Squonk42/USBug/CAM/D43324.TXT.pdf

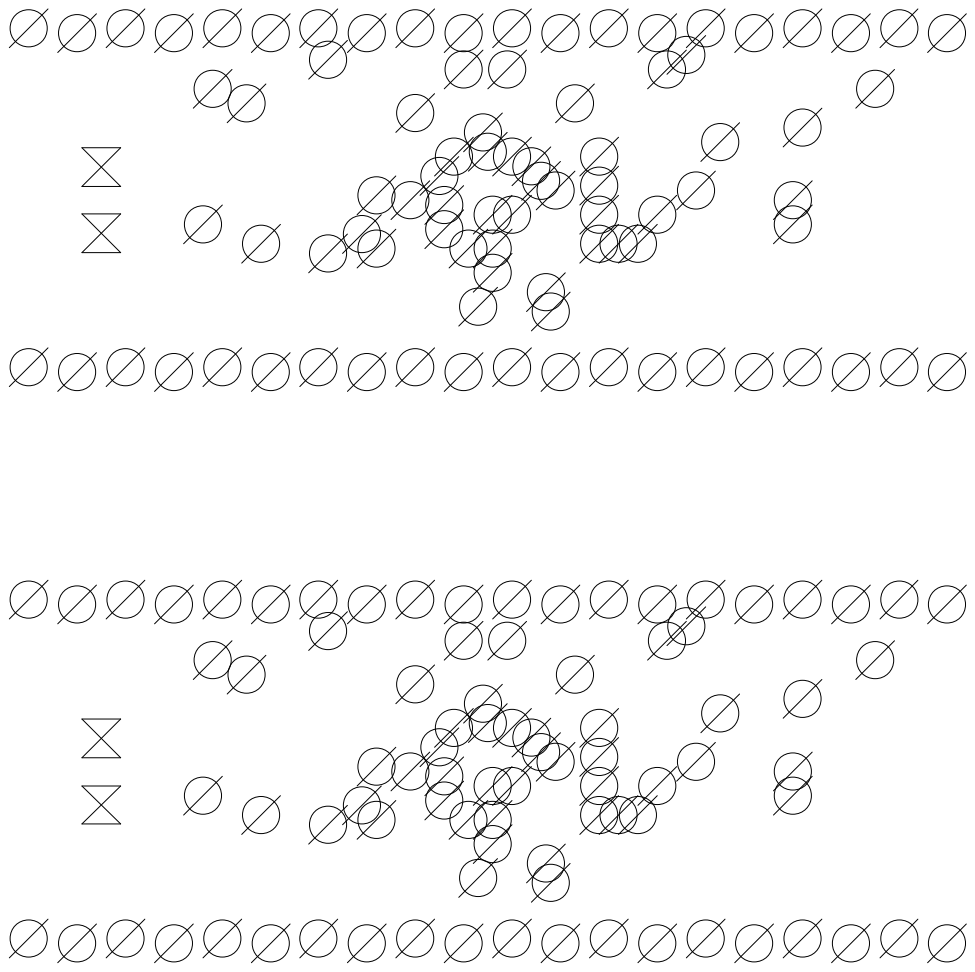
[picture p5: page 1]
