Squonk42/USBug/CAM/D43324.png

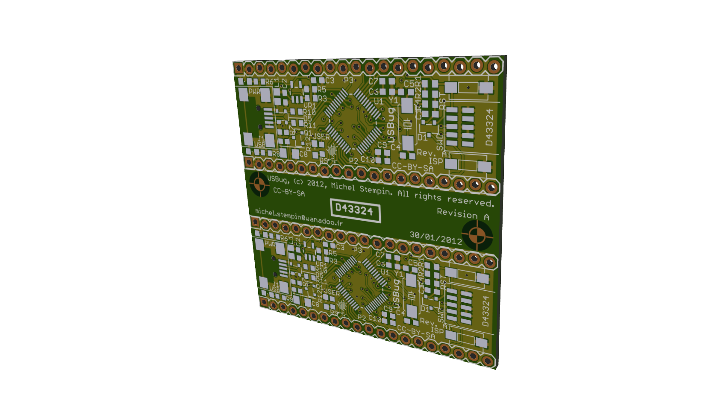
CAM/D43324.png
