Squonk42/USBug/eagleUp/Board-Comparison.jpg

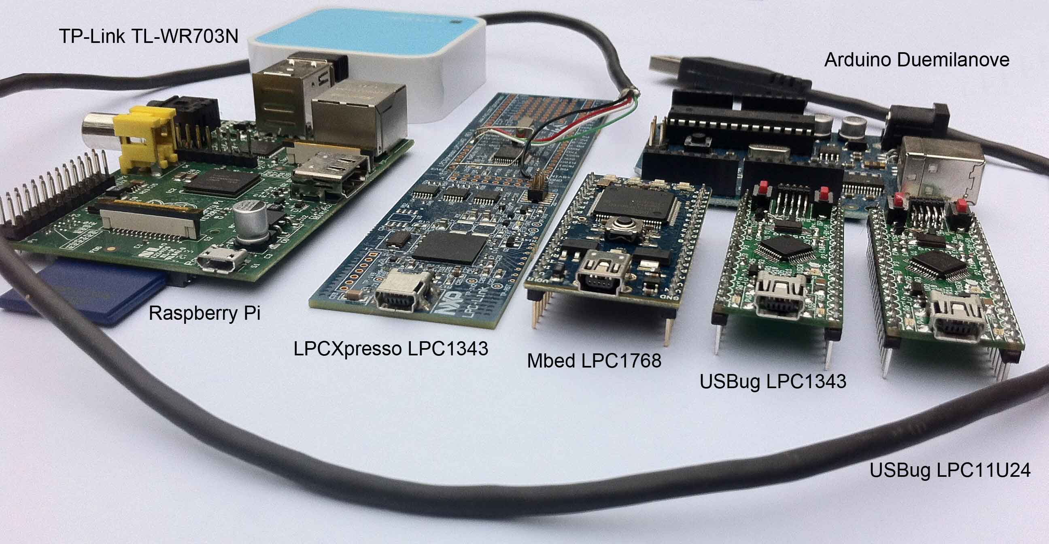
eagleUp/Board-Comparison.jpg
