Squonk42/USBug/eagleUp/eagleUp_USBug_board_bottom.jpg

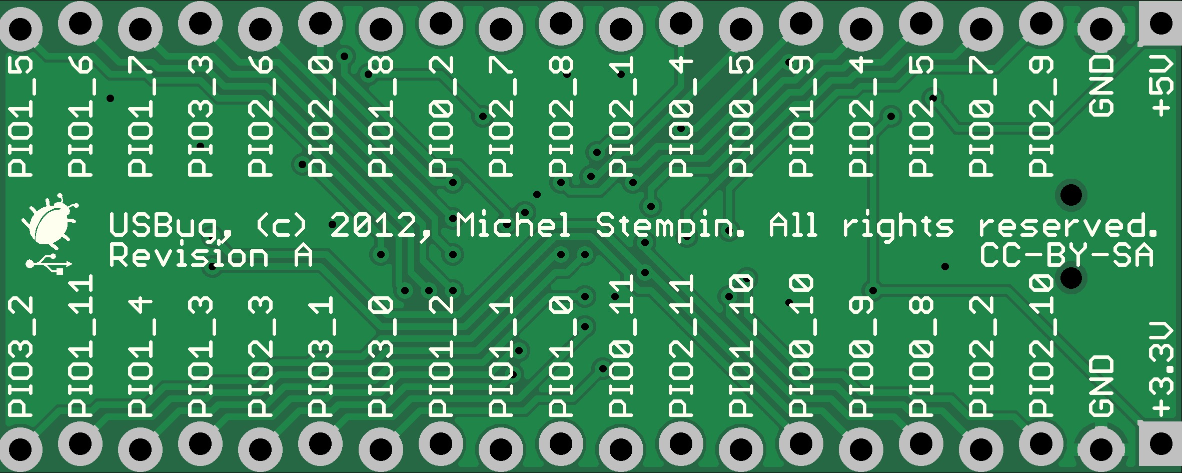
eagleUp/eagleUp_USBug_board_bottom.jpg
