Squonk42/USBug/eagleUp/eagleUp_USBug_board_bottom.png

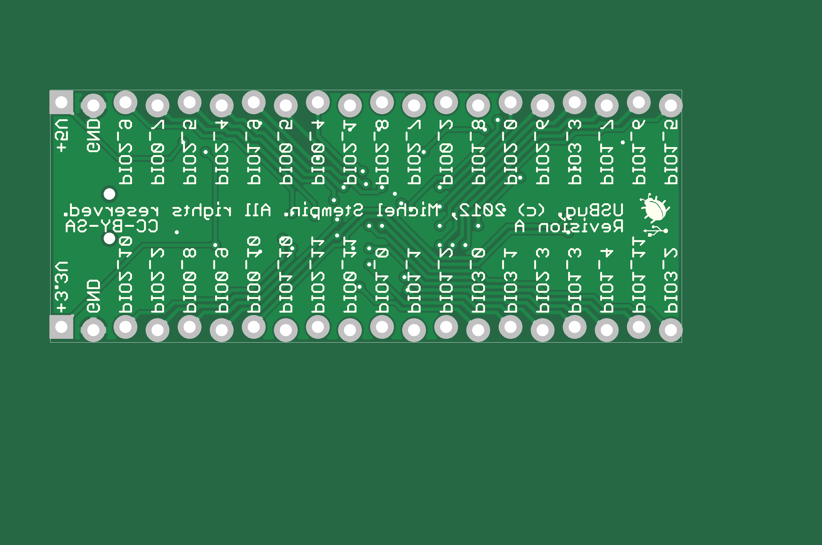
eagleUp/eagleUp_USBug_board_bottom.png
