Squonk42/USBug/eagleUp/eagleUp_USBug_board_top.jpg

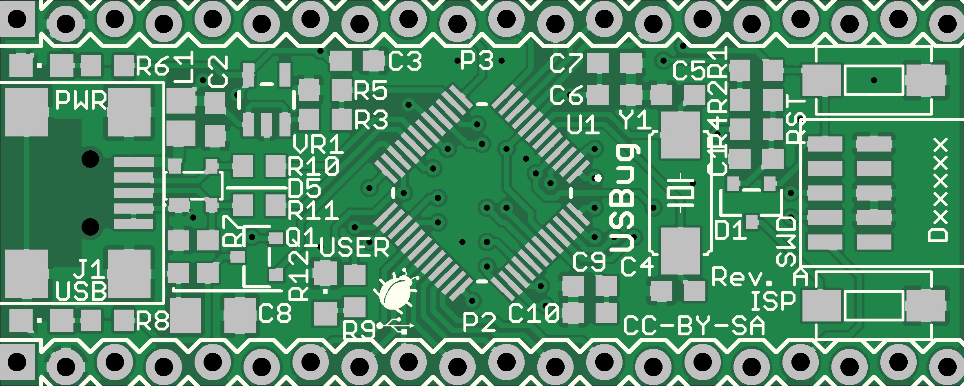
eagleUp/eagleUp_USBug_board_top.jpg
