Squonk42/USBug/eagleUp/eagleUp_USBug_board_top.png

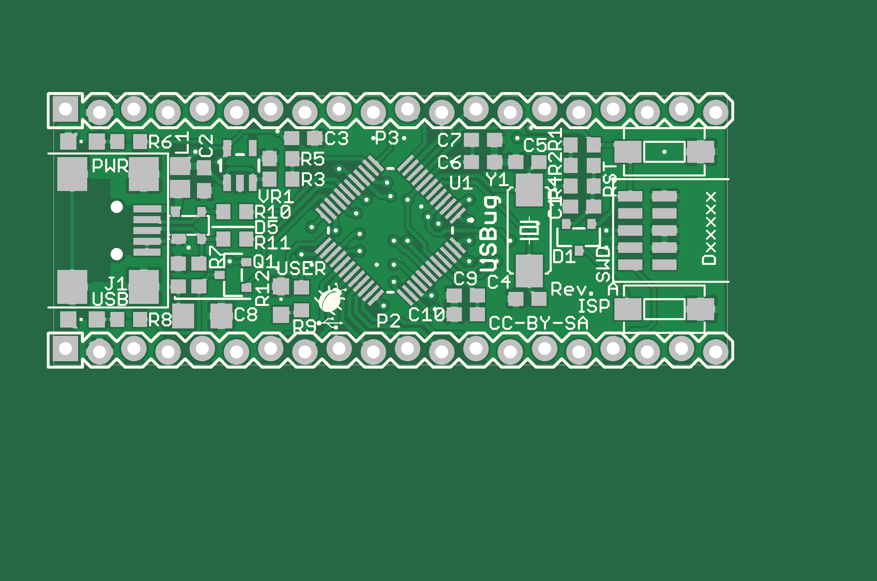
eagleUp/eagleUp_USBug_board_top.png
