Squonk42/USBug/eagleUp/eagleUp_USBug_bottom.png

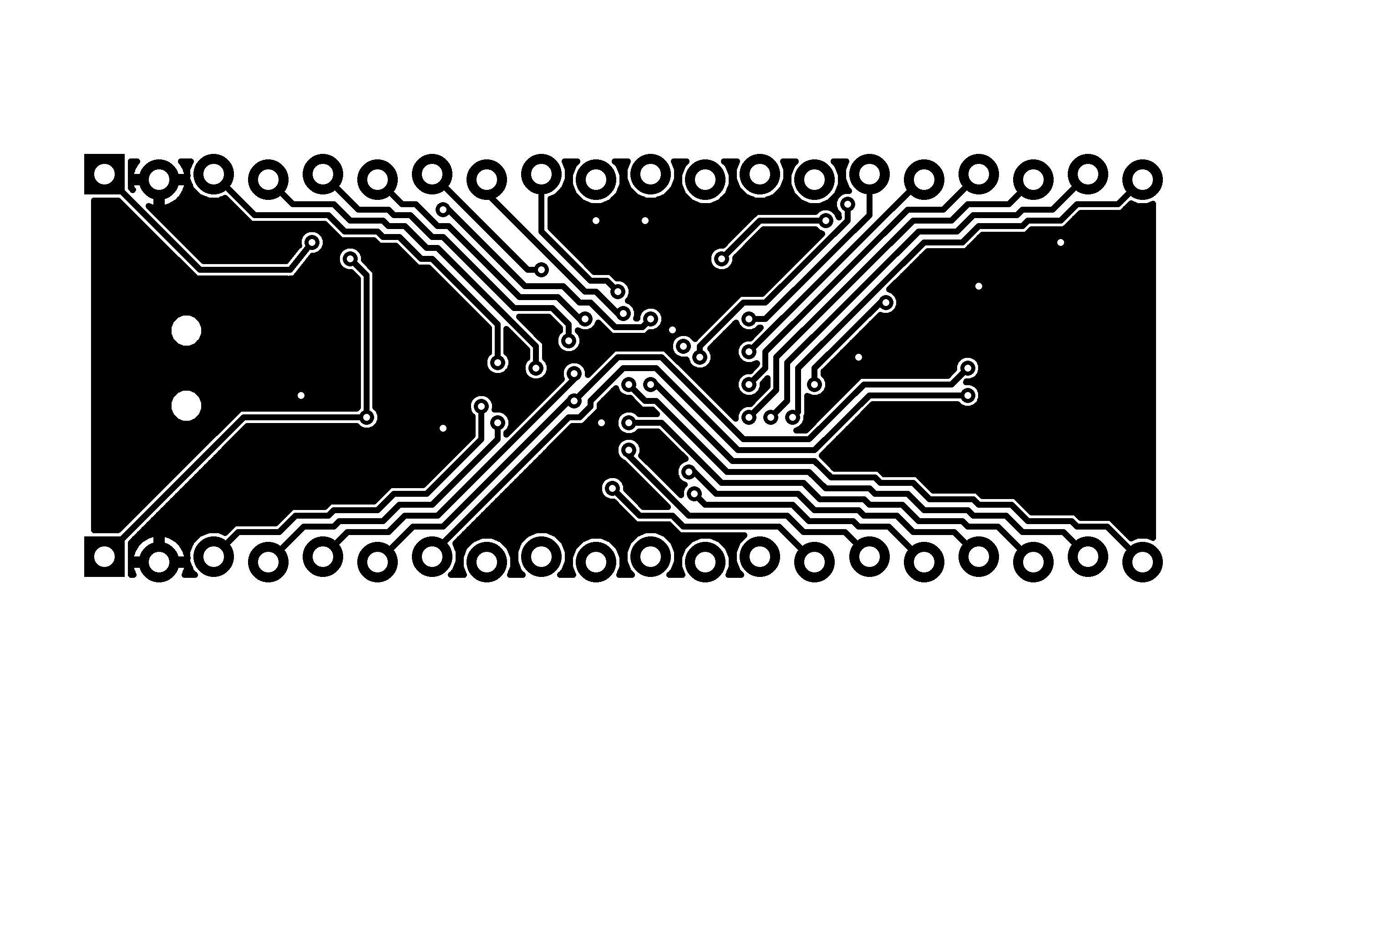
eagleUp/eagleUp_USBug_bottom.png
