Squonk42/USBug/eagleUp/eagleUp_USBug_bottom_mask.png

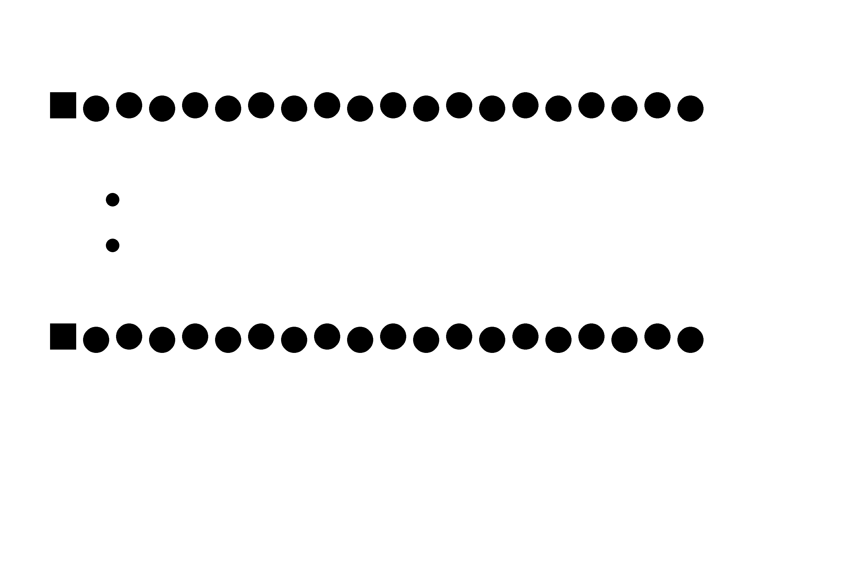
eagleUp/eagleUp_USBug_bottom_mask.png
