Squonk42/USBug/eagleUp/eagleUp_USBug_bottom_silk.png

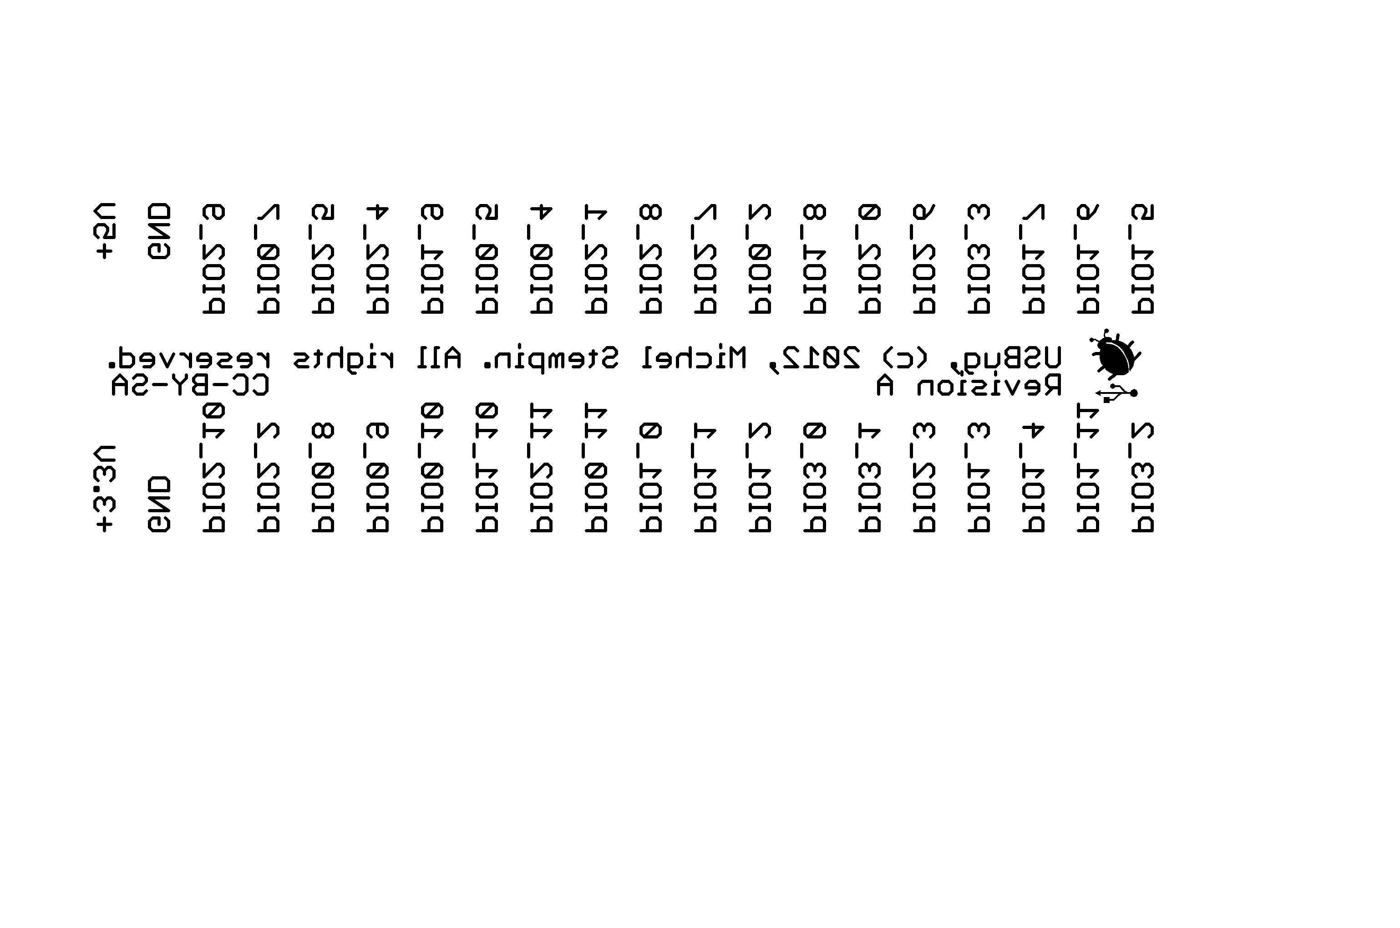
eagleUp/eagleUp_USBug_bottom_silk.png
