Squonk42/USBug/eagleUp/eagleUp_USBug_drill.png

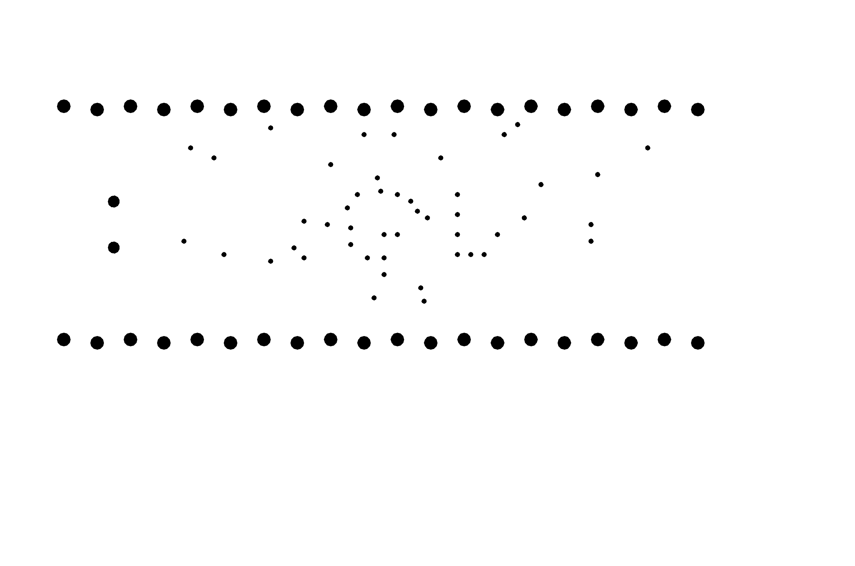
eagleUp/eagleUp_USBug_drill.png
