Squonk42/USBug/eagleUp/eagleUp_USBug_imagesize.png

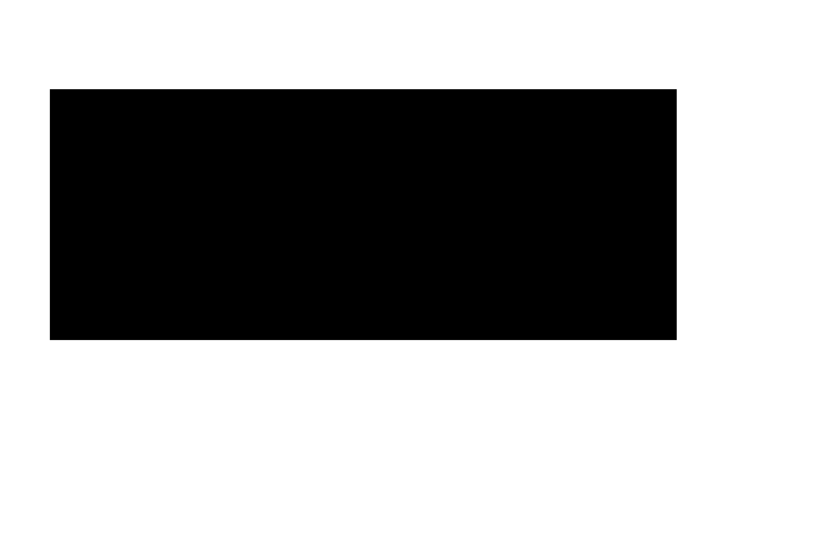
eagleUp/eagleUp_USBug_imagesize.png
