Squonk42/USBug/eagleUp/eagleUp_USBug_outline.png

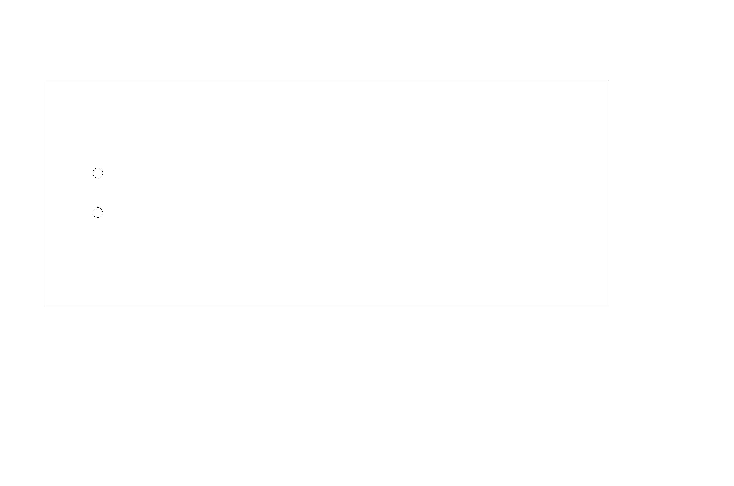
eagleUp/eagleUp_USBug_outline.png
