Squonk42/USBug/eagleUp/eagleUp_USBug_top.png

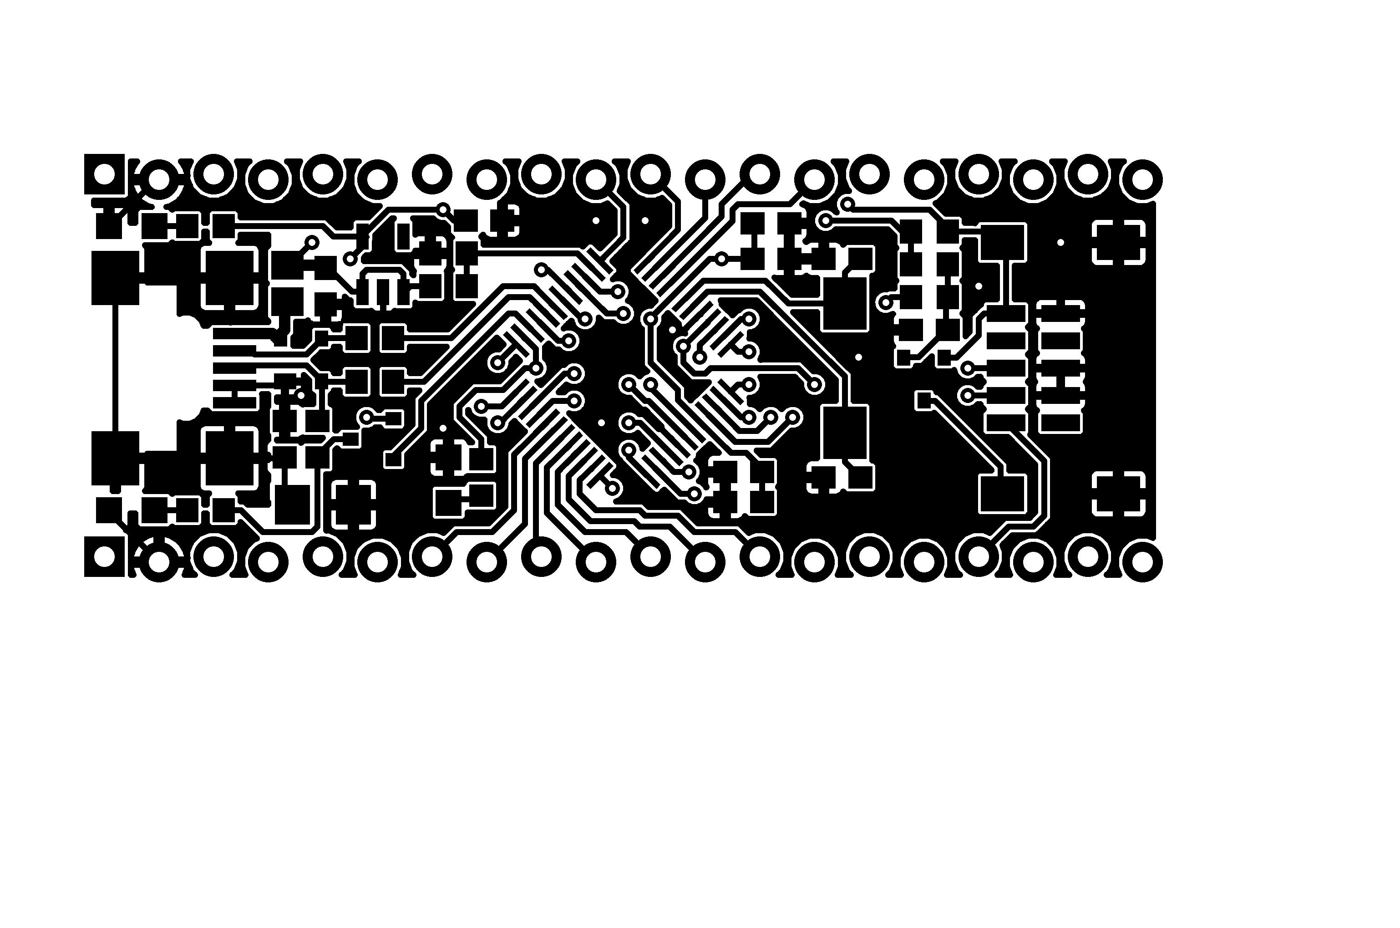
eagleUp/eagleUp_USBug_top.png
