Squonk42/USBug/eagleUp/eagleUp_USBug_top_mask.png

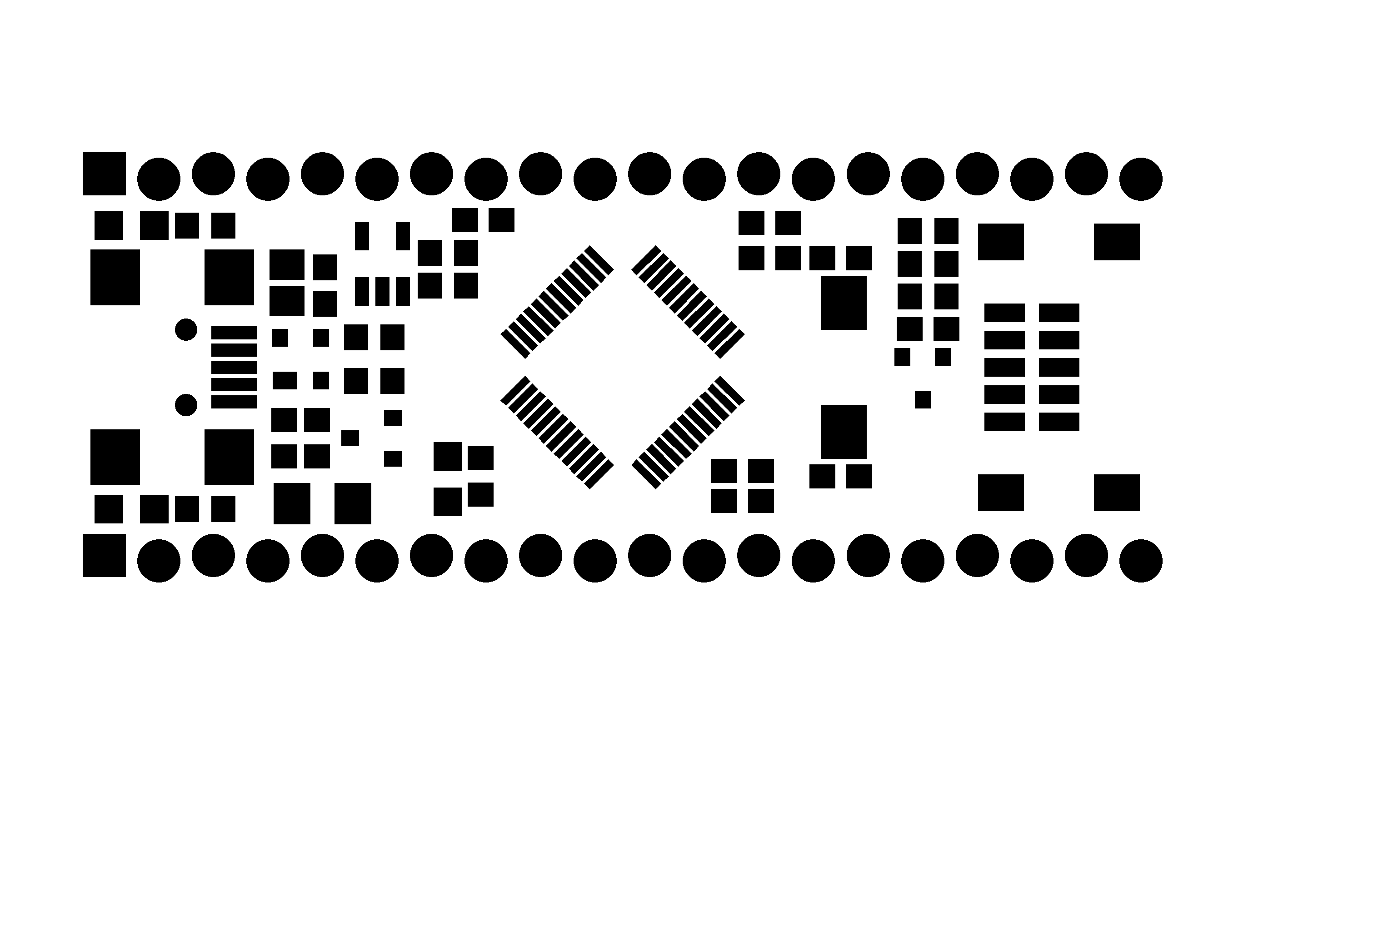
eagleUp/eagleUp_USBug_top_mask.png
