Squonk42/USBug/eagleUp/eagleUp_USBug_top_silk.png

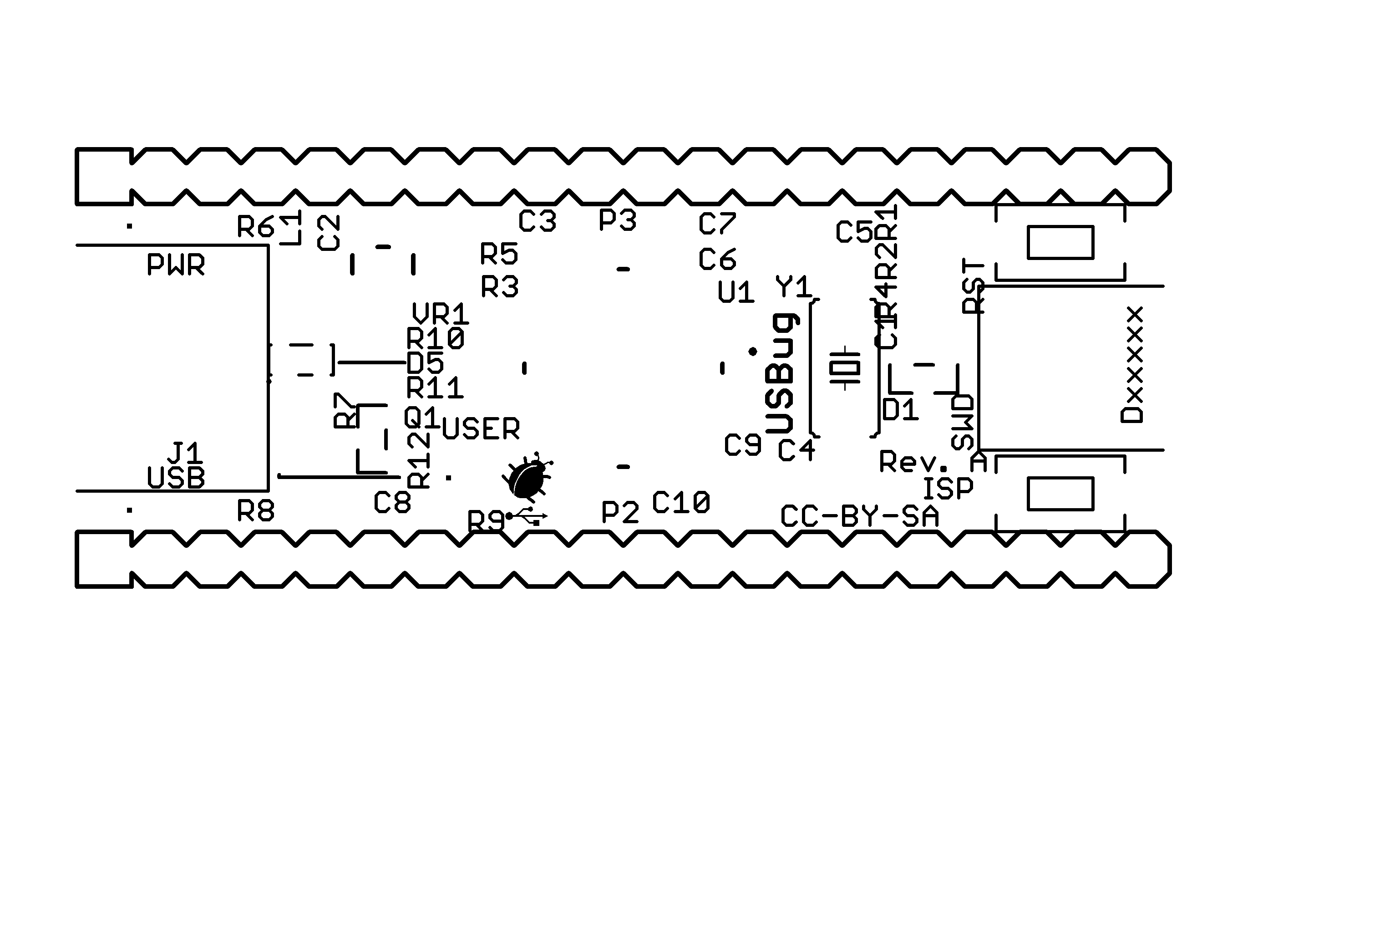
eagleUp/eagleUp_USBug_top_silk.png
