Squonk42/USBug/eagleUp/USBug1.jpg

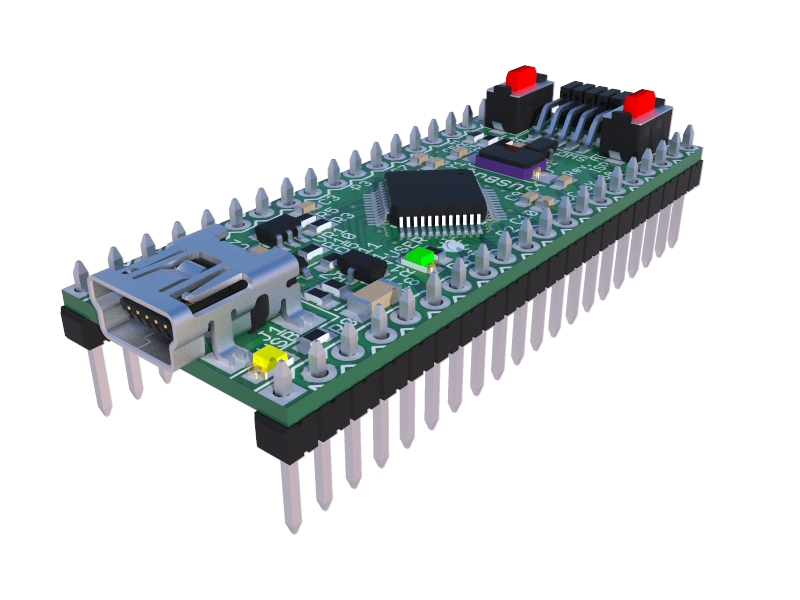
eagleUp/USBug1.jpg
