Squonk42/USBug/eagleUp/USBug2.jpg

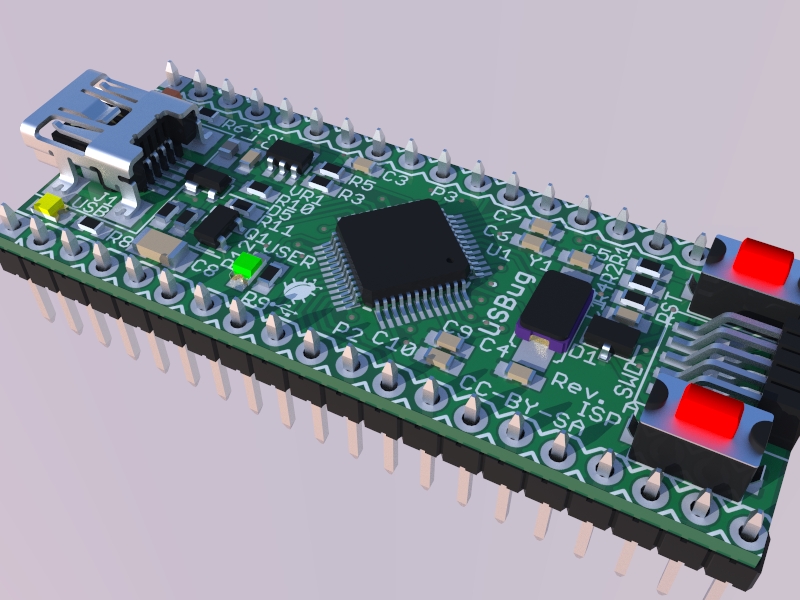
eagleUp/USBug2.jpg
