Squonk42/USBug/eagleUp/USBug2_mask.jpg

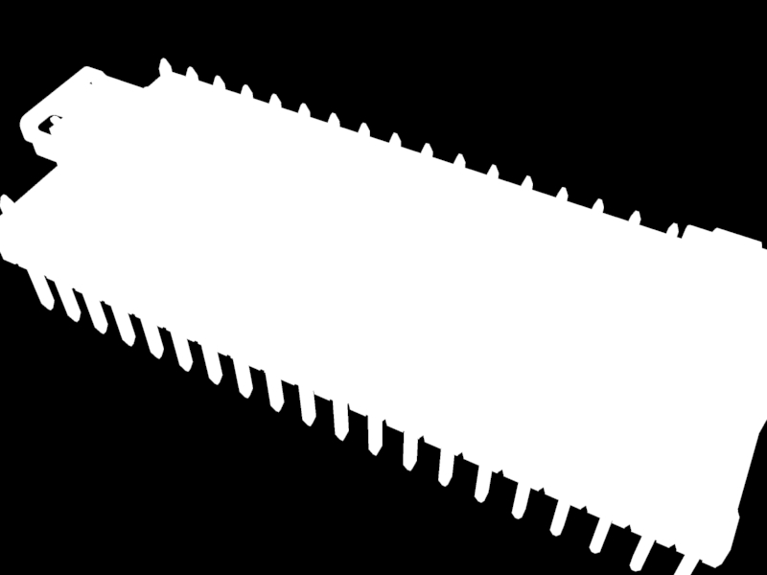
eagleUp/USBug2_mask.jpg
