Squonk42/USBug/eagleUp/USBug3.jpg

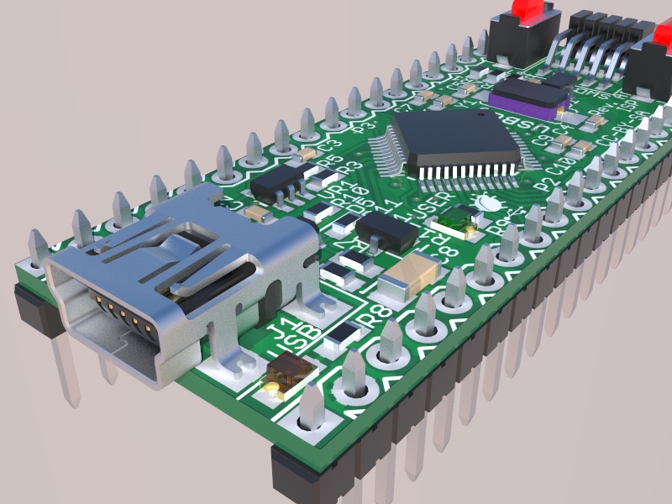
eagleUp/USBug3.jpg
