Squonk42/USBug/eagleUp/USBug3_mask.jpg

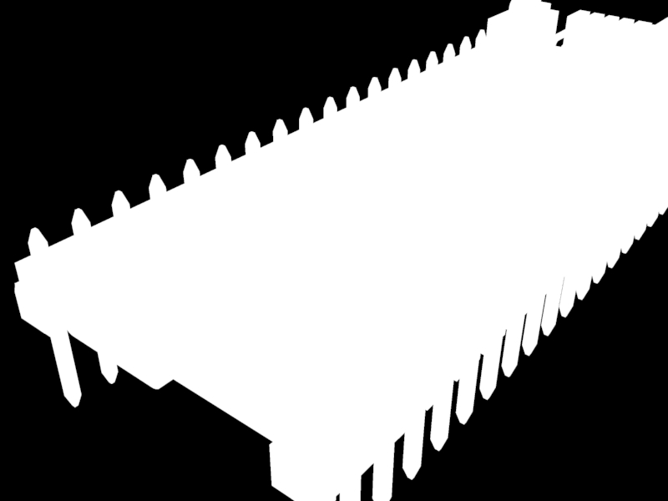
eagleUp/USBug3_mask.jpg
