Squonk42/USBug/eagleUp/USBug4.jpg

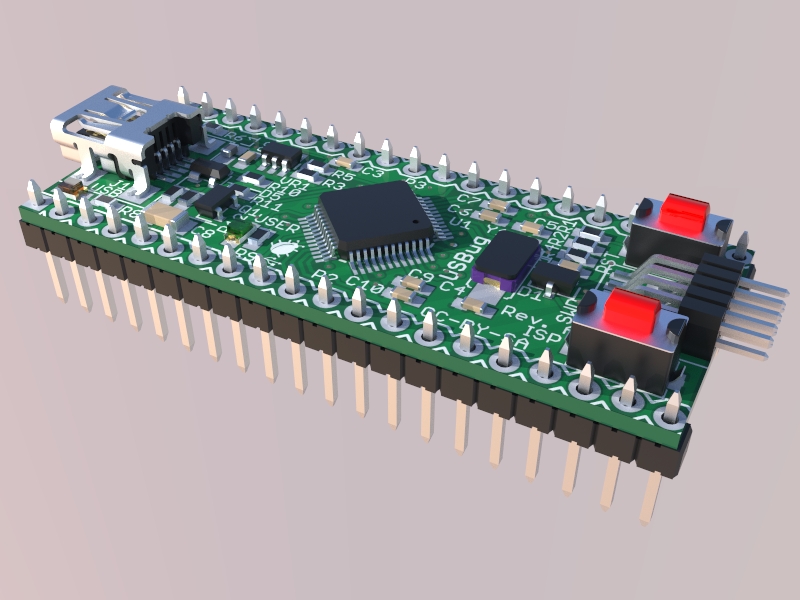
eagleUp/USBug4.jpg
