Squonk42/USBug/eagleUp/USBug4_mask.jpg

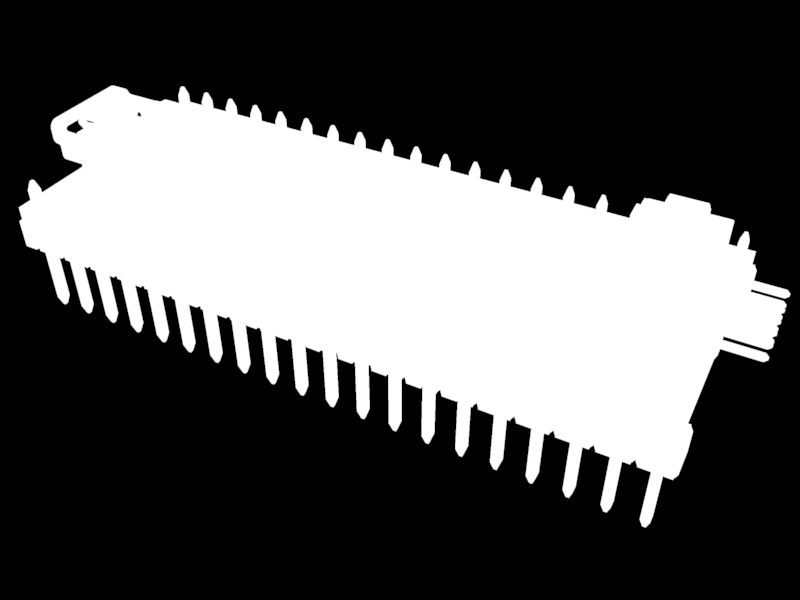
eagleUp/USBug4_mask.jpg
