Squonk42/USBug/eagleUp/USBug/eagleUp_USBug_board_bottom.png

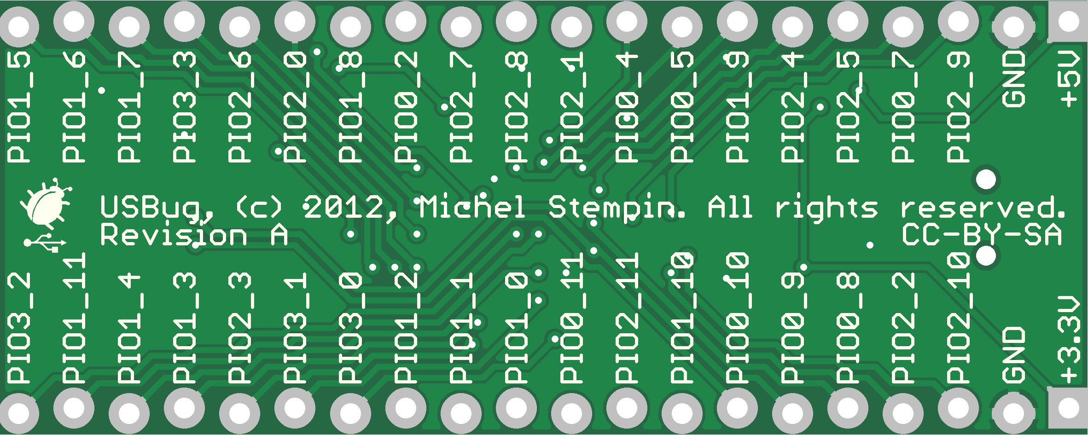
eagleUp/USBug/eagleUp_USBug_board_bottom.png
