Squonk42/USBug/eagleUp/USBug/eagleUp_USBug_board_top.png

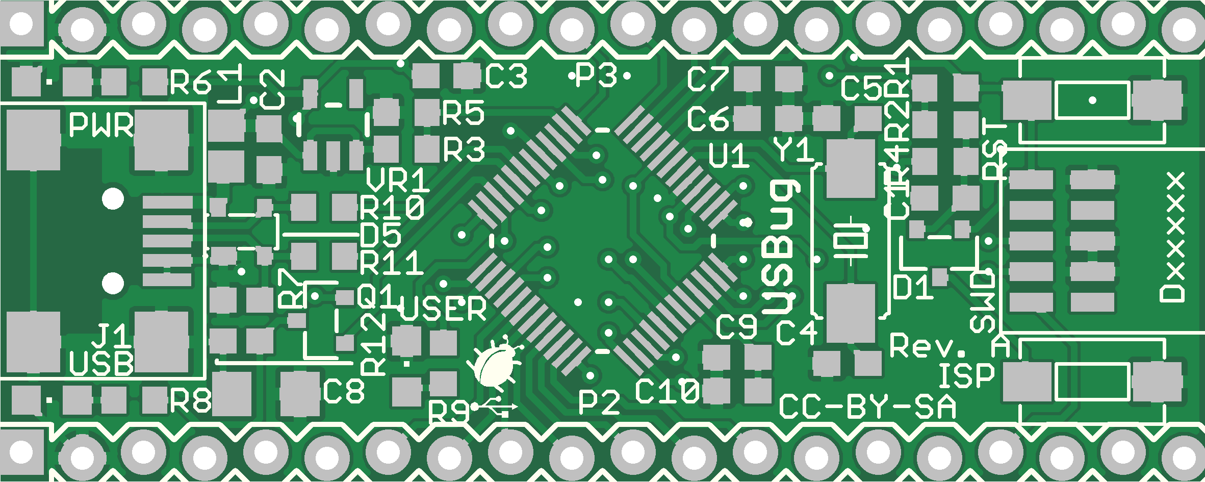
eagleUp/USBug/eagleUp_USBug_board_top.png
