Squonk42/USBug/eagleUp/USBug/USBug.png

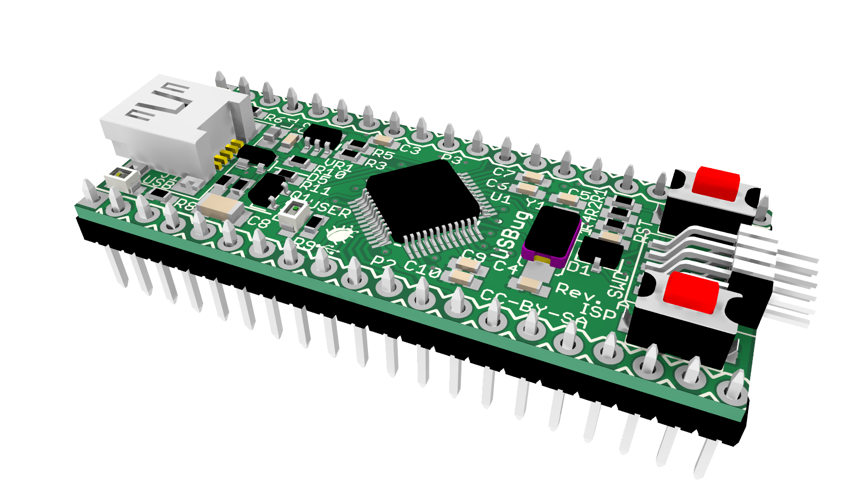
eagleUp/USBug/USBug.png
