Squonk42/USBug/eagleUp/USBug/UXgaMBfST.jpg

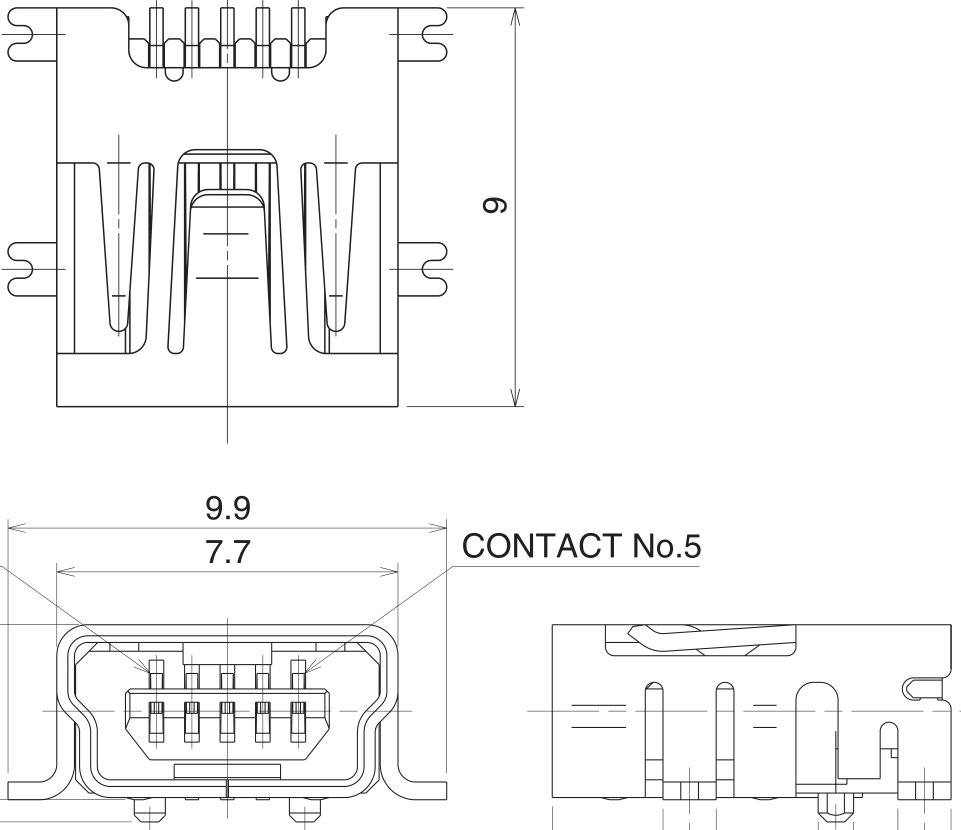
eagleUp/USBug/UXgaMBfST.jpg
