Squonk42/USBug/eagleUp/USBug_HiRes_Layout.png

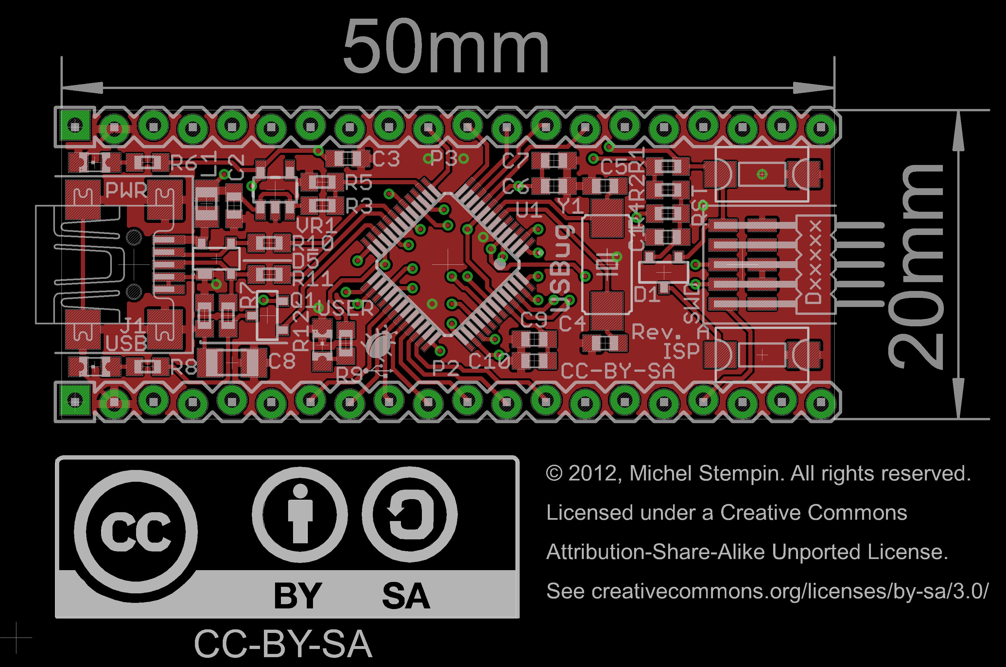
eagleUp/USBug_HiRes_Layout.png
