Squonk42/USBug/eagleUp/USBug_KT2.jpg

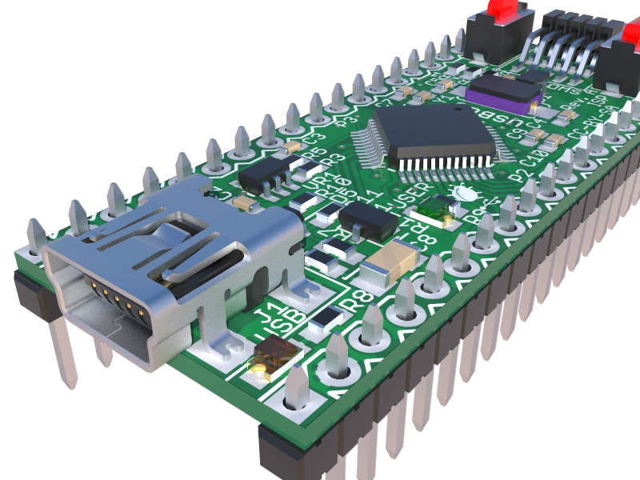
eagleUp/USBug_KT2.jpg
