Squonk42/USBug/eagleUp/USBug_KT.jpg

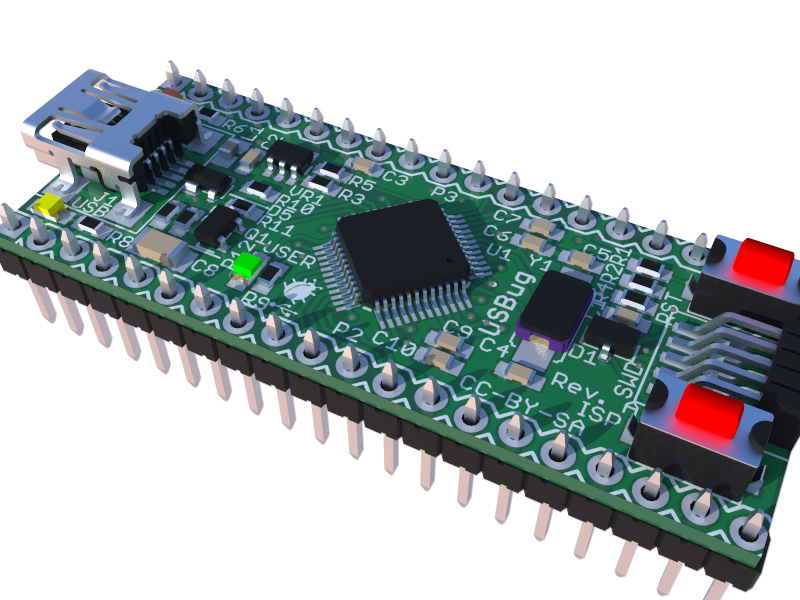
eagleUp/USBug_KT.jpg
