Squonk42/USBug/eagleUp/USBug_mask.jpg

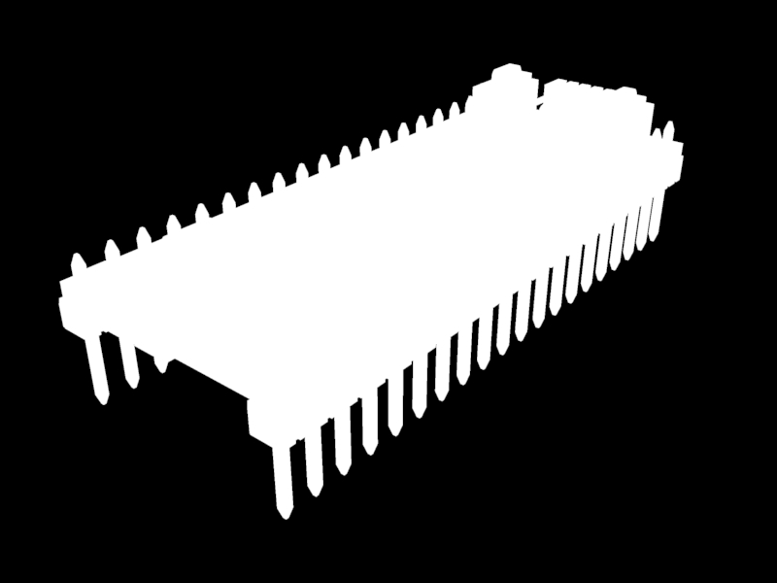
eagleUp/USBug_mask.jpg
