Squonk42/USBug/CAM/D43324.GTS.pdf

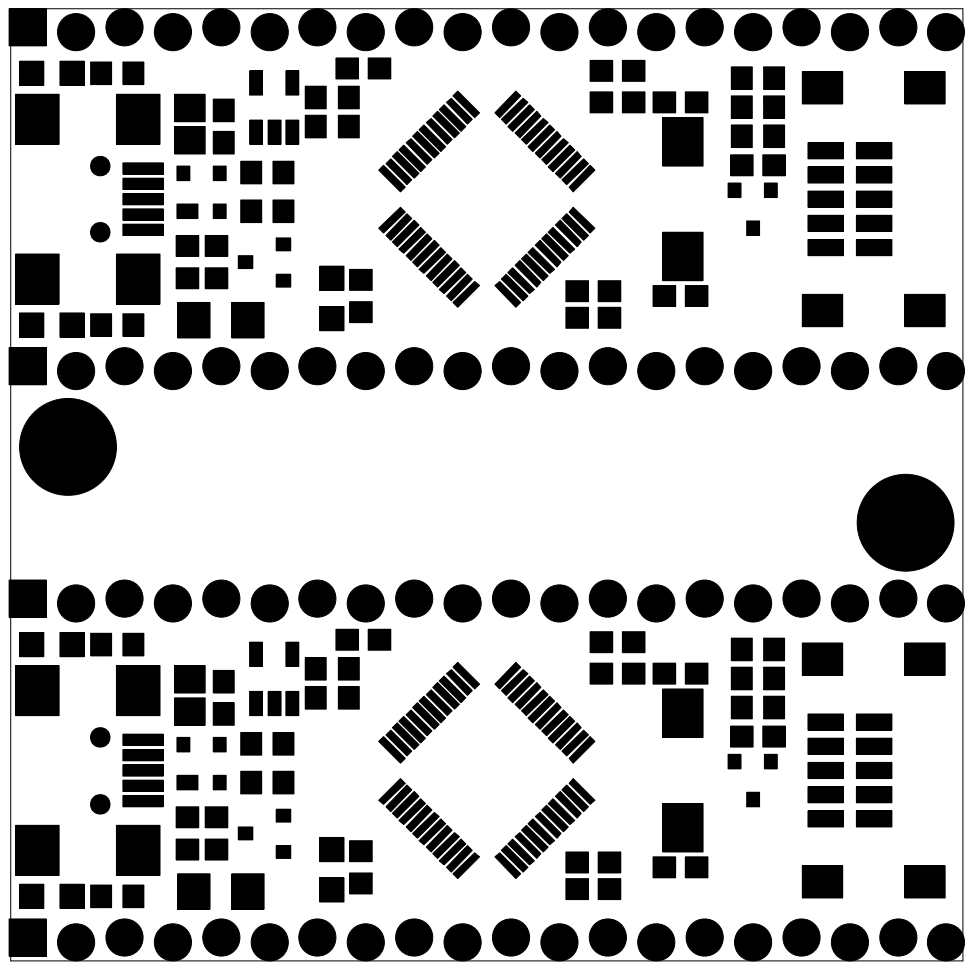
[picture p47: page 1]
